haum/axihaum/A_T_T.fcstd

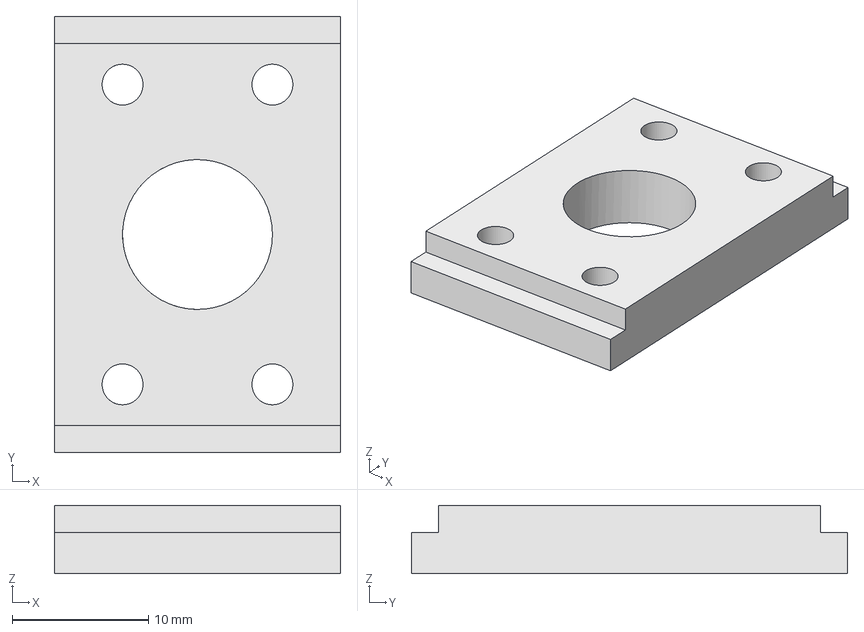
[picture p15: CAD file, 2014-04-27]
A_T_T.fcstd
21.0 x 32.0 x 5.00 mm
