haum/axihaum/A_T_LR.fcstd

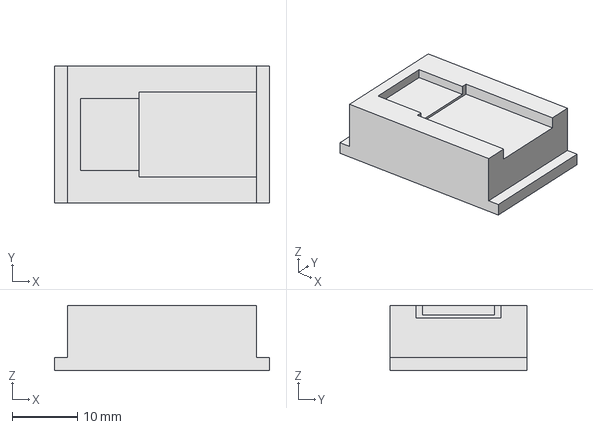
[picture p16: CAD file, 2014-04-27]
A_T_LR.fcstd
33.0 x 21.0 x 10.0 mm
