haum/axihaum/A_C_NEMA23.FCStd

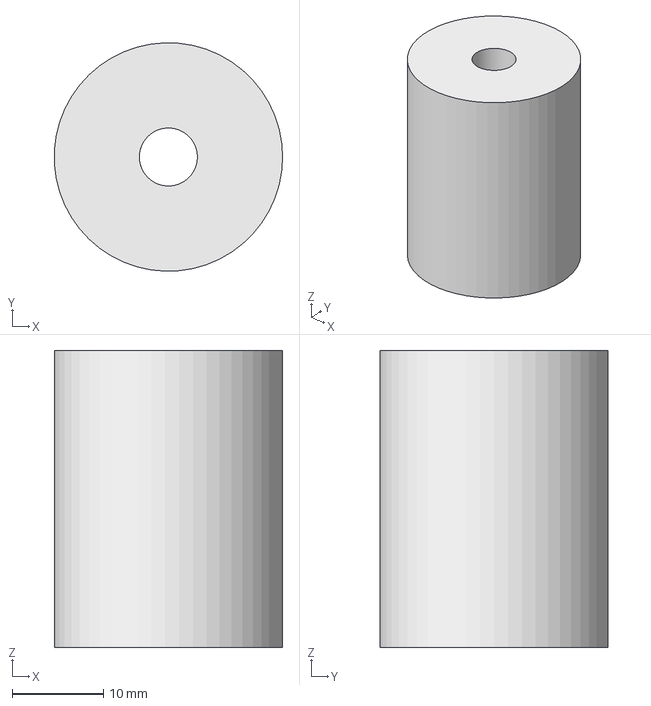
[picture p17: CAD file, 2014-04-27]
A_C_NEMA23.FCStd
25.0 x 25.0 x 32.5 mm
