haum/axihaum/A_M.fcstd

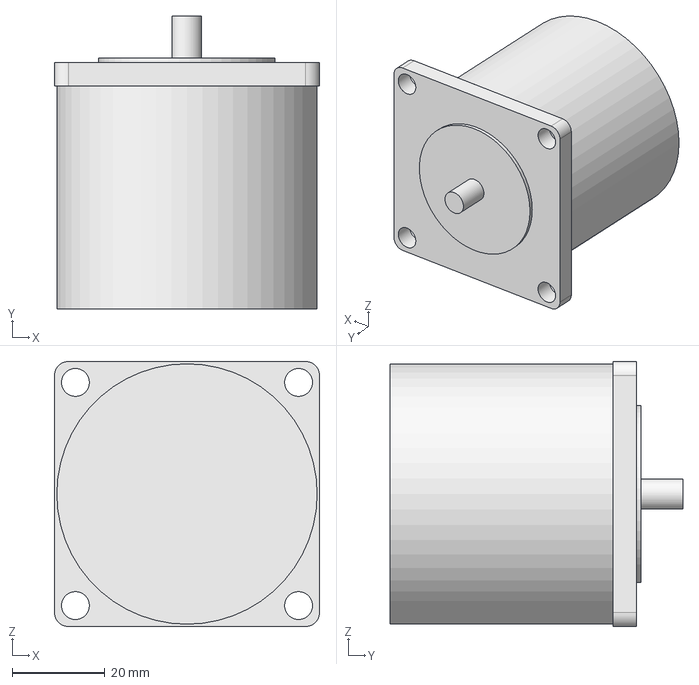
[picture p18: CAD file, 2014-03-28]
A_M.fcstd
57.0 x 63.0 x 57.0 mm
