haum/axihaum/LPKS_ProtoMat_91s.fcstd

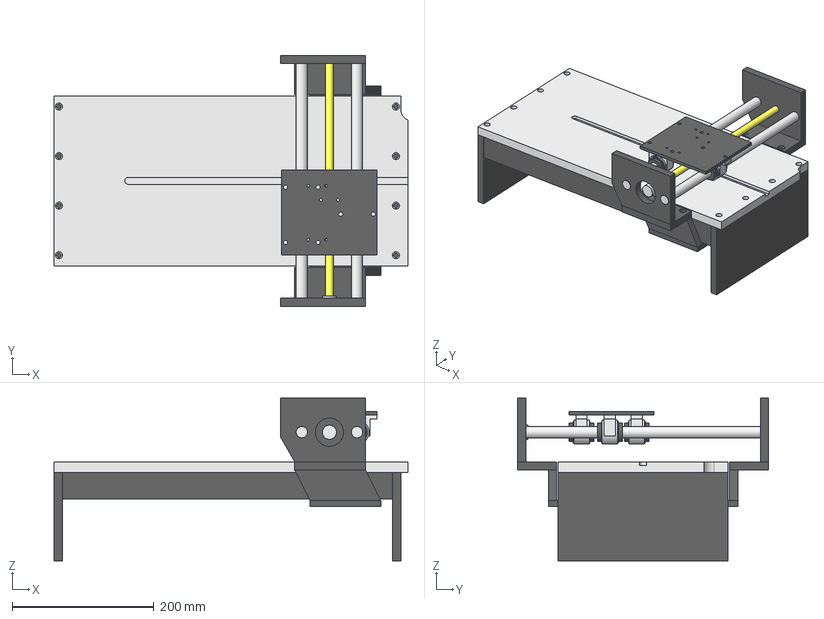
[picture p20: CAD file, 2014-03-24]
LPKS_ProtoMat_91s.fcstd
500.0 x 355.0 x 229.7 mm
Y_P_L
Y_G_U
Y_G_D
Y_P_R
Y_SC
Y_S
A_LB_Y0_alu
A_LB_Y0_plastic
A_LB_Y1_plastic
A_LB_Y1_alu
A_LB_Y2_plastic
A_LB_Y2_alu
X_SY_RT
X_SY_LT
X_SY_LM
X_SY_RM
X_SY_B
C_T
C_B
C_F
X Axis
Z_P
