haum/axihaum/Z_S.fcstd

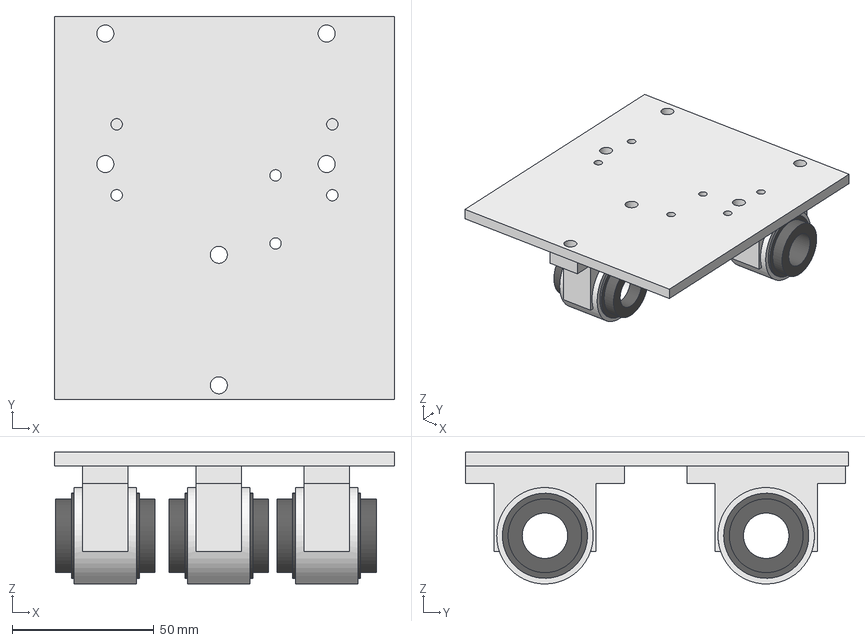
[picture p21: CAD file, 2014-03-24]
Z_S.fcstd
120.0 x 135.0 x 46.5 mm
alu001
flasque plastique
flasque plastique001
alu002
flasque plastique002
alu003
