haum/axihaum/Z_P.fcstd

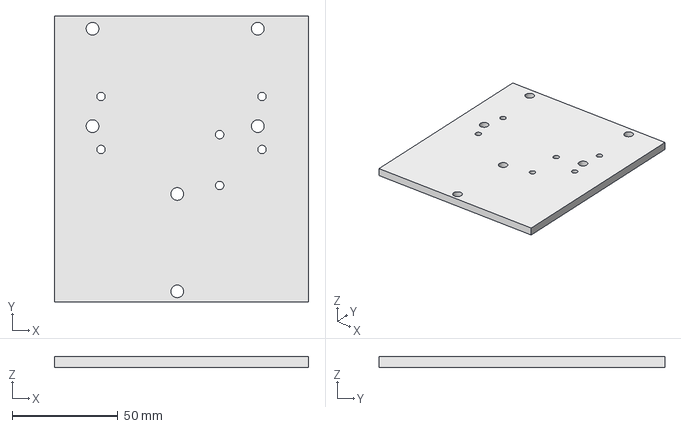
[picture p22: CAD file, 2014-03-24]
Z_P.fcstd
120.0 x 135.0 x 5.00 mm
