haum/axihaum/A_LB.fcstd

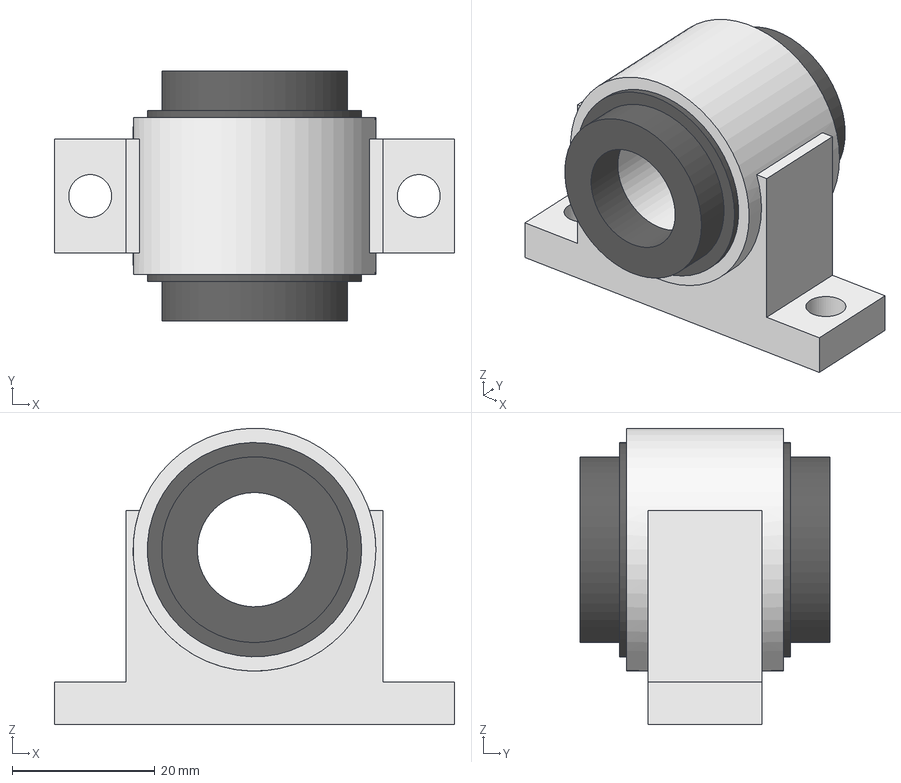
[picture p23: CAD file, 2014-03-24]
A_LB.fcstd
56.0 x 35.0 x 41.5 mm
flasque plastique
alu
