haum/axihaum/C_T.FCStd

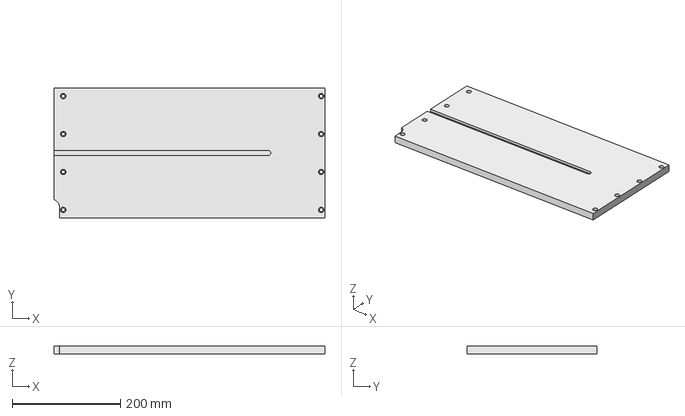
[picture p24: CAD file, 2014-03-23]
C_T.FCStd
500.0 x 240.0 x 14.7 mm
