haum/axihaum/X_SY_B.dxf

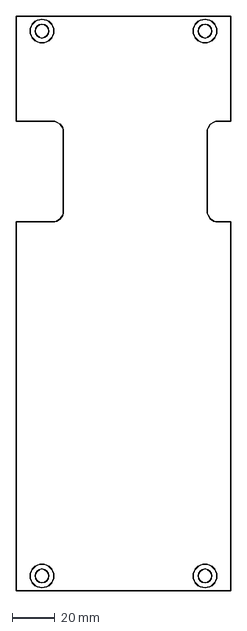
[picture p25: CAD file, 2014-03-21]
X_SY_B.dxf
100.0 x 268.0 mm
