haum/axihaum/X_SY_RT.dxf

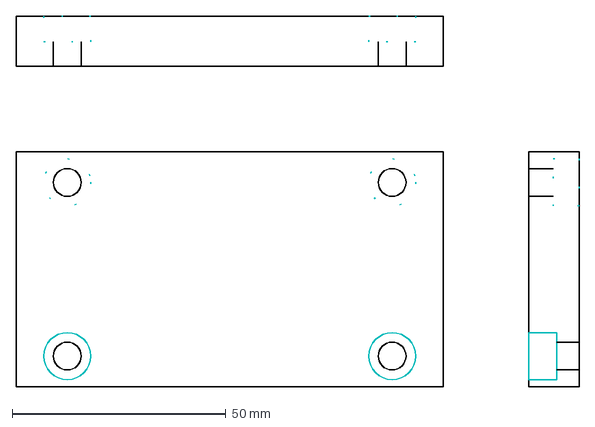
[picture p26: CAD file, 2014-03-21]
X_SY_RT.dxf
131.7 x 86.7 mm
