haum/axihaum/X_SY_RM.dxf

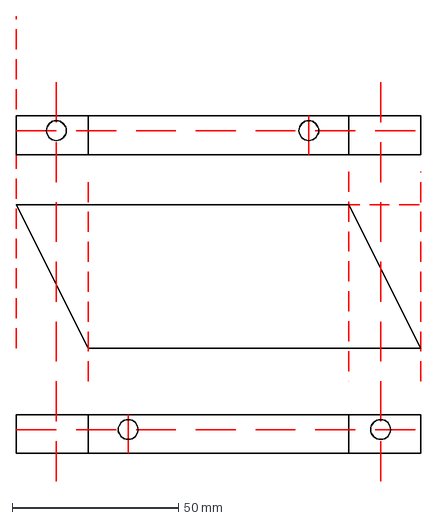
[picture p27: CAD file, 2014-03-21]
X_SY_RM.dxf
121.6 x 140.0 mm
