haum/axihaum/X_SY_LM.dxf

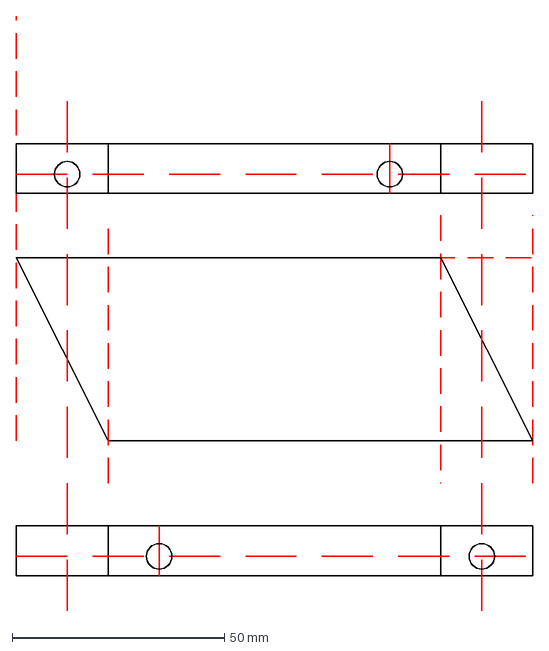
[picture p28: CAD file, 2014-03-21]
X_SY_LM.dxf
121.6 x 140.0 mm
