haum/axihaum/Y_P_R.dxf

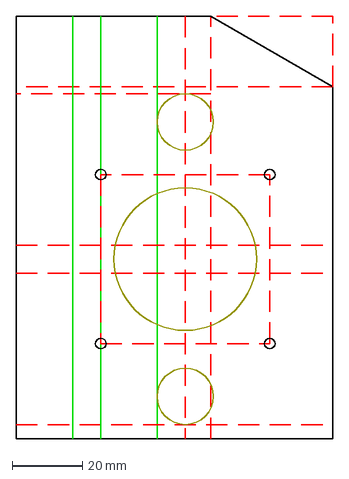
[picture p29: CAD file, 2014-03-20]
Y_P_R.dxf
89.9 x 120.0 mm
