haum/axihaum/Y_P_L.dxf

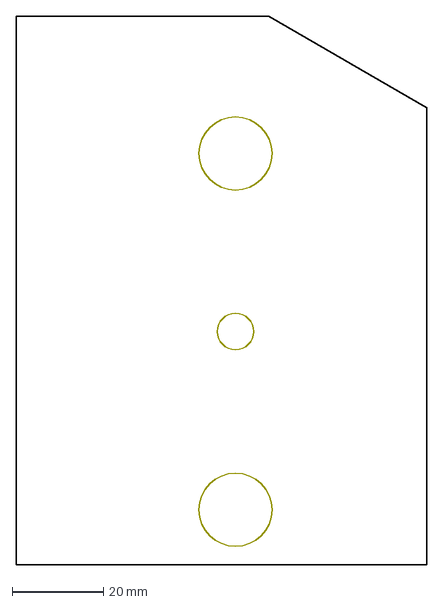
[picture p30: CAD file, 2014-03-20]
Y_P_L.dxf
89.9 x 120.0 mm
